vasya-zh/kampela-soldering-kit/kicad/base-board/images/base-board.png

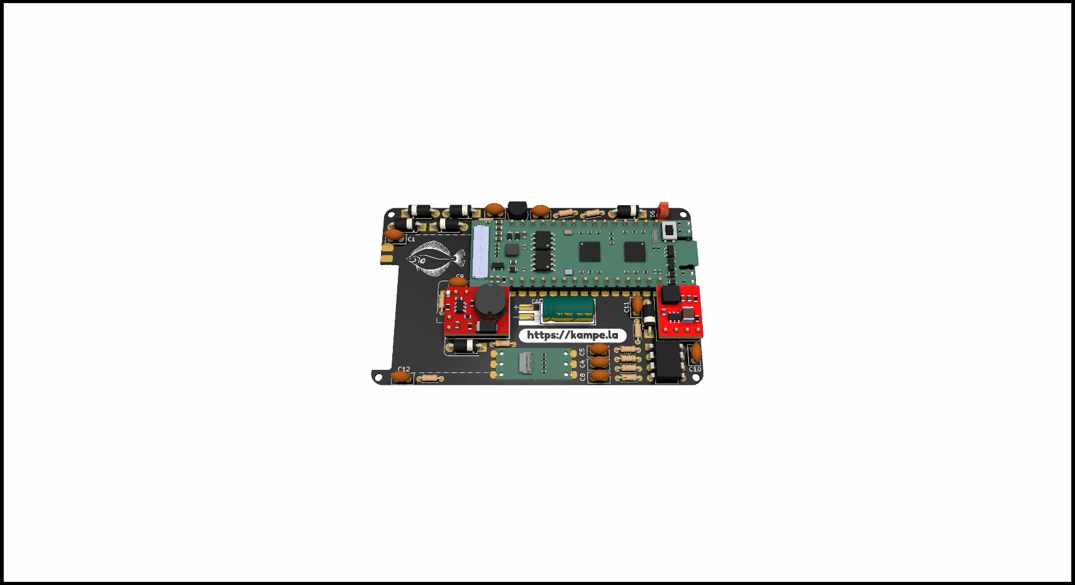
kicad/base-board/images/base-board.png
