vasya-zh/kampela-soldering-kit/kicad/base-board/images/bottom.png

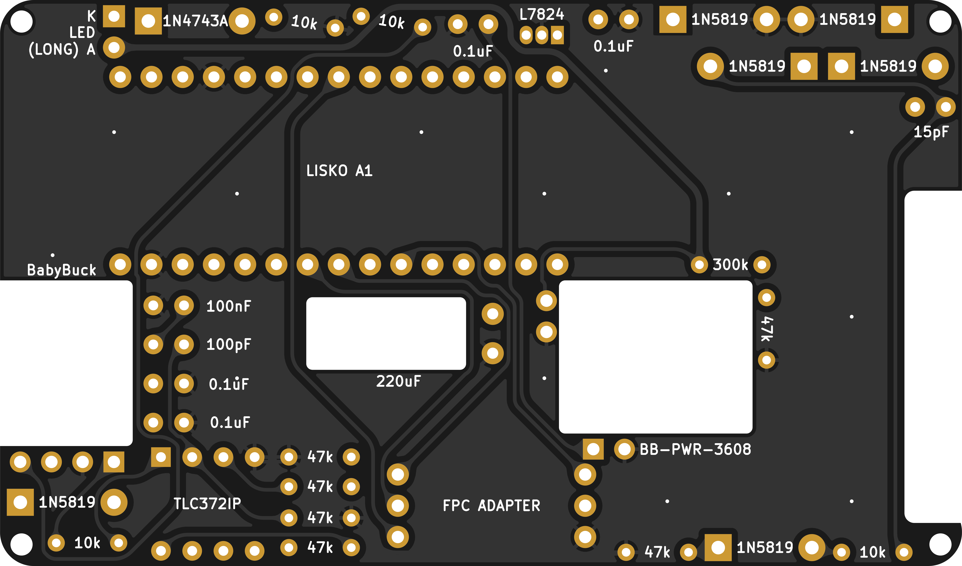
kicad/base-board/images/bottom.png
