vasya-zh/kampela-soldering-kit/kicad/base-board/images/top.png

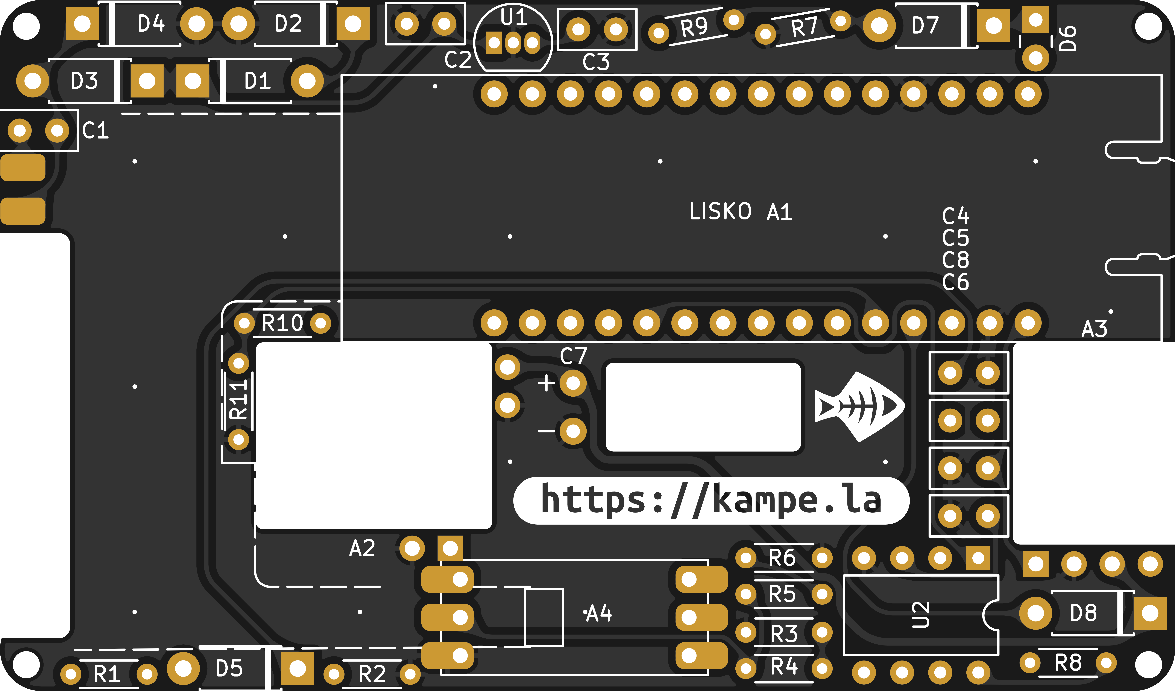
kicad/base-board/images/top.png
