vasya-zh/kampela-soldering-kit/kicad/flex-coil8/images/bottom.png

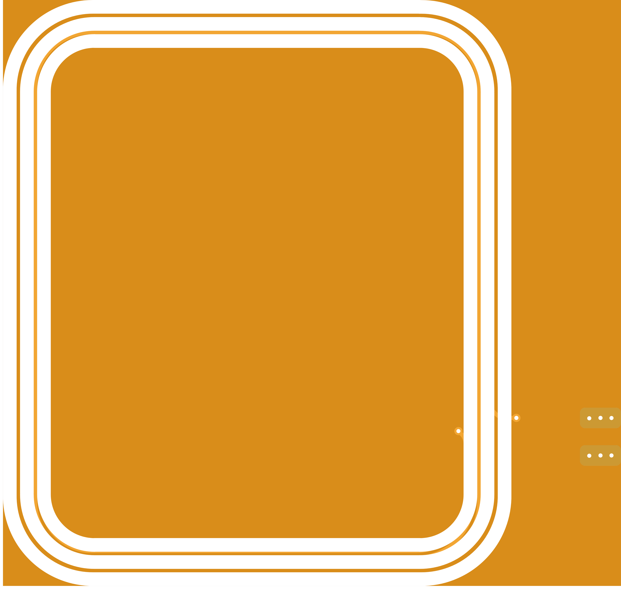
kicad/flex-coil8/images/bottom.png
