vasya-zh/kampela-soldering-kit/kicad/flex-coil8/images/flex-coil8.png

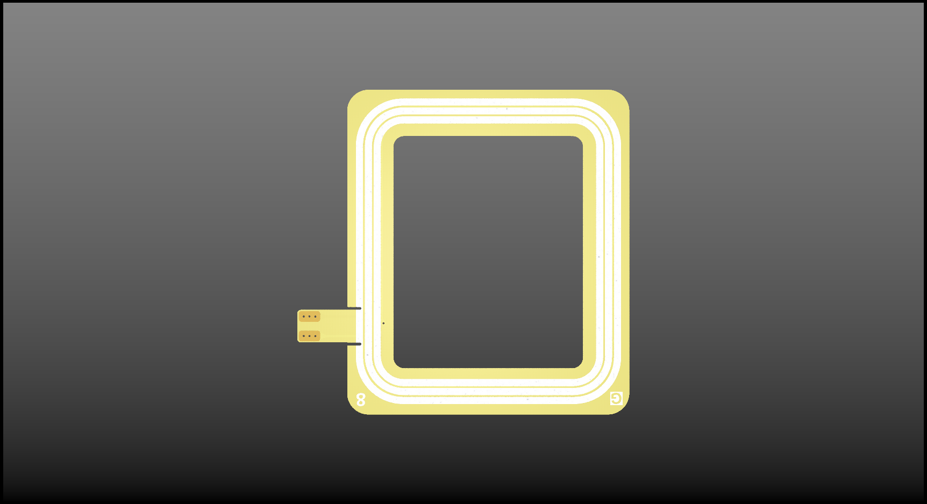
kicad/flex-coil8/images/flex-coil8.png
