vasya-zh/kampela-soldering-kit/kicad/flex-coil8/images/top.png

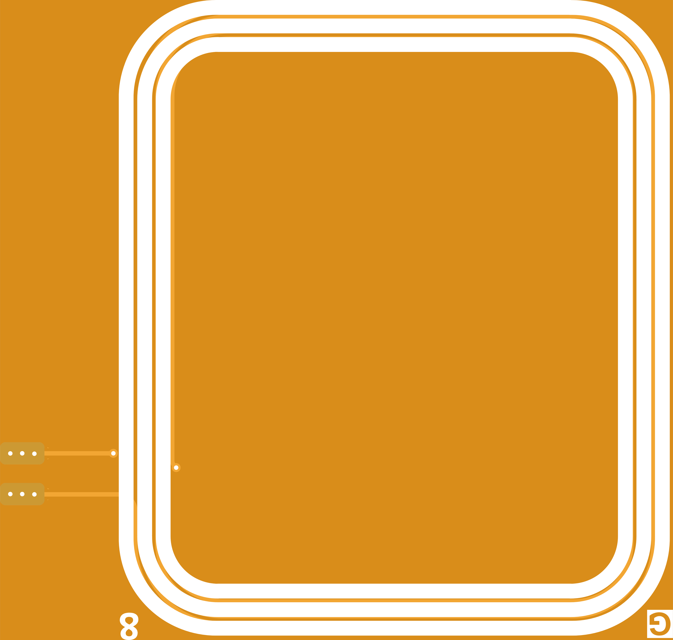
kicad/flex-coil8/images/top.png
