vasya-zh/kampela-soldering-kit/kicad/tag/images/bottom.png

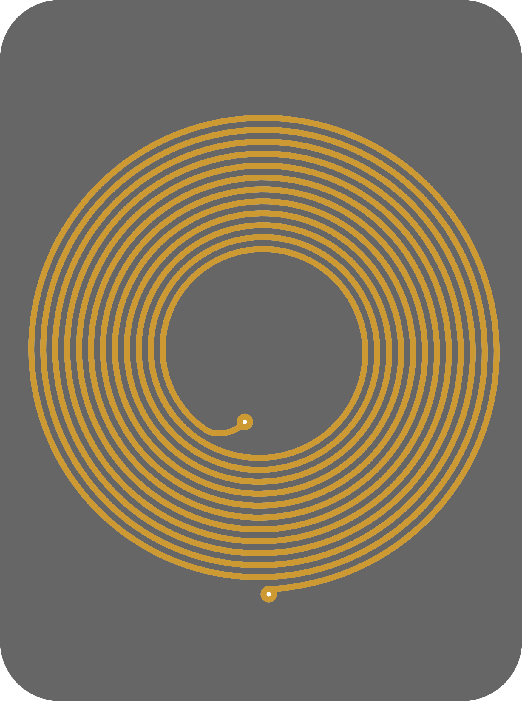
kicad/tag/images/bottom.png
