vasya-zh/kampela-soldering-kit/kicad/tag/images/top.png

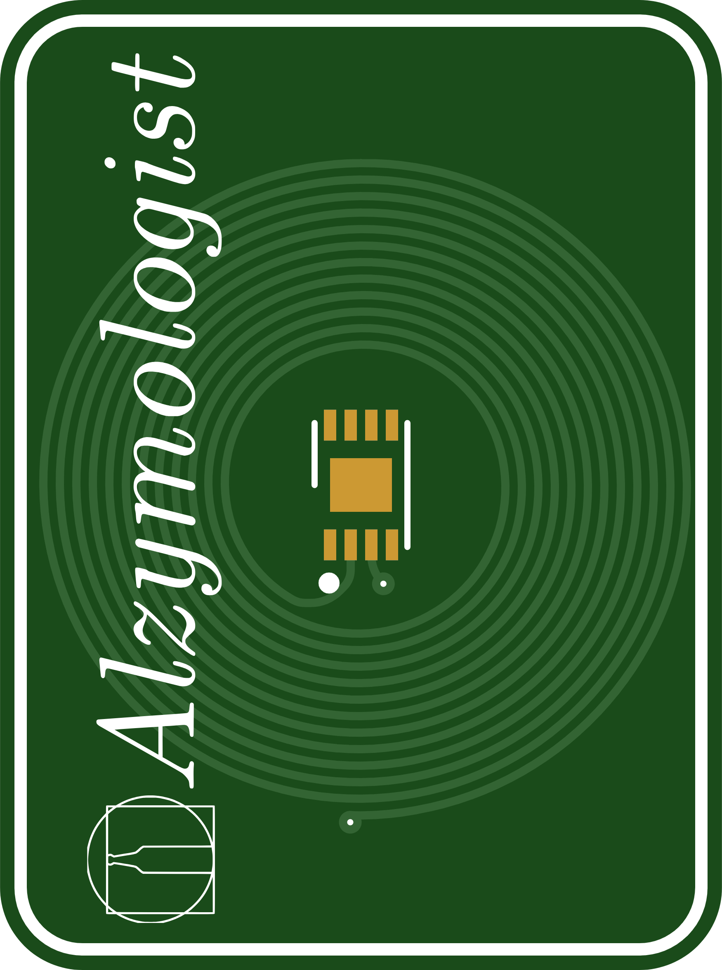
kicad/tag/images/top.png
