vasya-zh/kampela-soldering-kit/kicad/touch-6pin-adapter/images/bottom.png

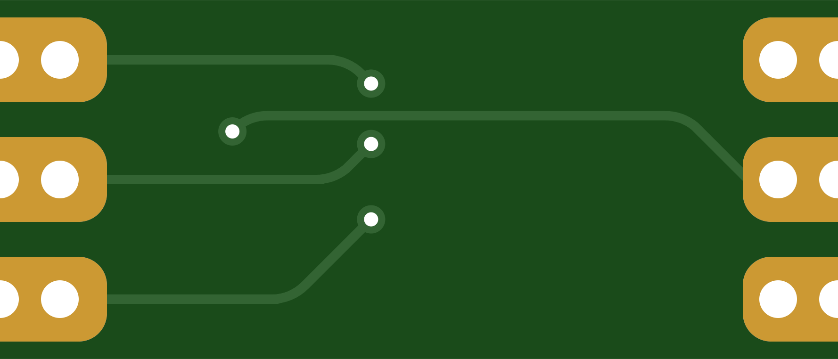
kicad/touch-6pin-adapter/images/bottom.png
