vasya-zh/kampela-soldering-kit/kicad/touch-6pin-adapter/images/top.png

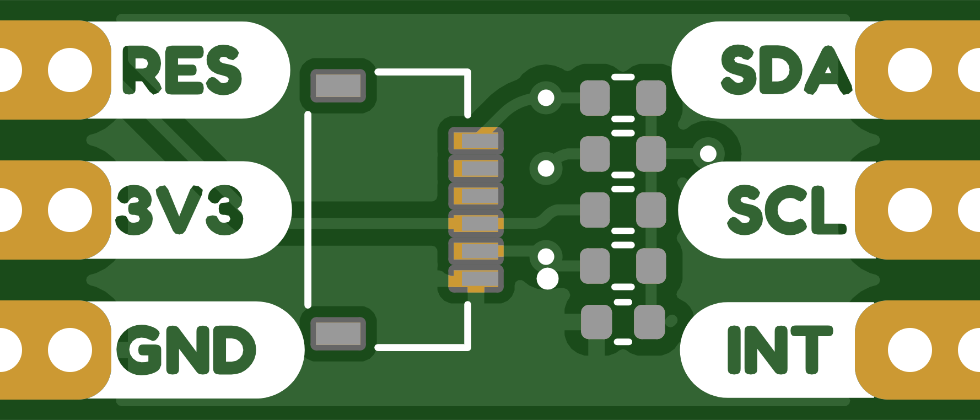
kicad/touch-6pin-adapter/images/top.png
