vasya-zh/kampela-soldering-kit/kicad/touch-6pin-adapter/images/touch-6pin-adapter.png

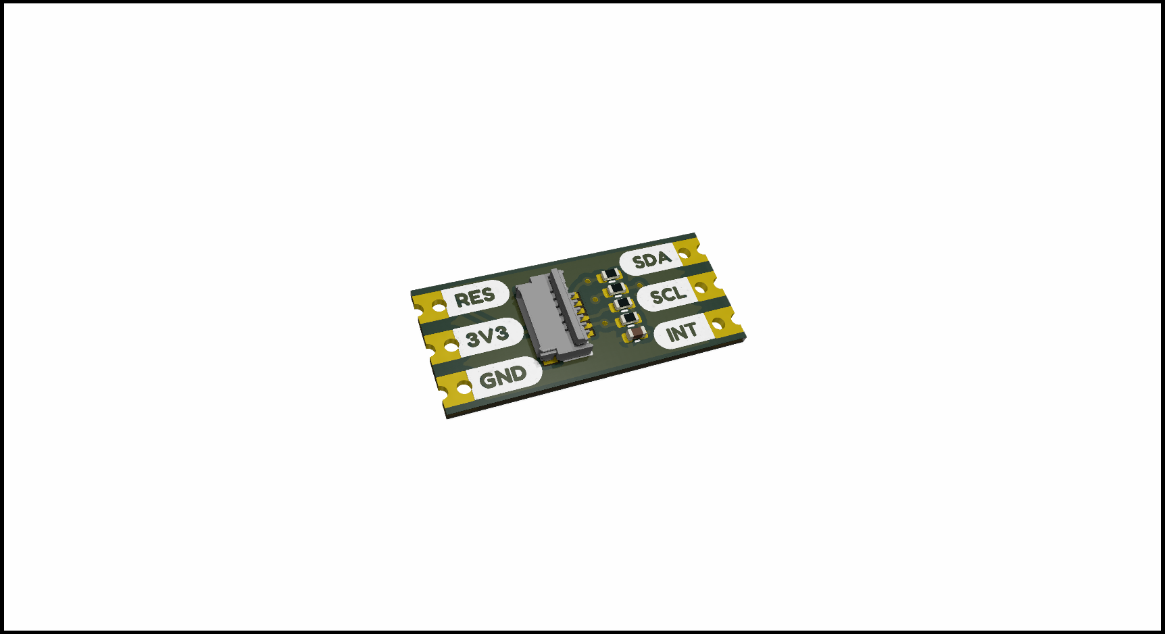
kicad/touch-6pin-adapter/images/touch-6pin-adapter.png
