vasya-zh/kampela-soldering-kit/kicad/base-board/images/02_base-board-power-modules-installed.png

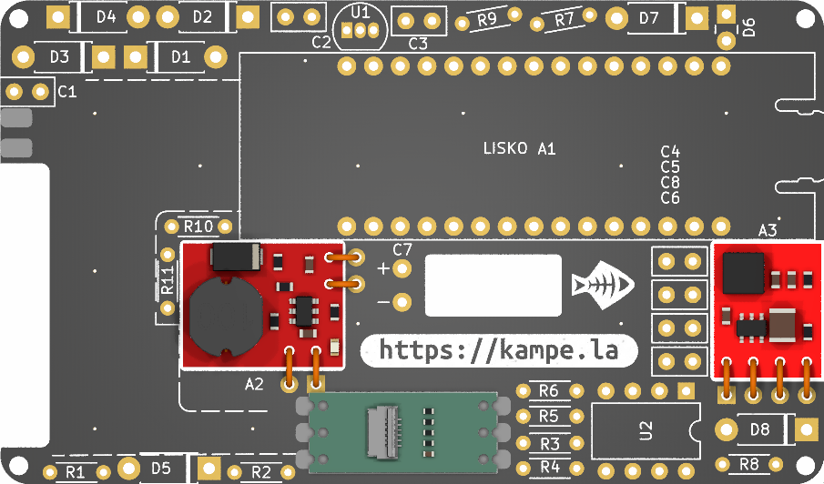
kicad/base-board/images/02_base-board-power-modules-installed.png
