vasya-zh/kampela-soldering-kit/kicad/base-board/images/06_base-board-IC-installed.png

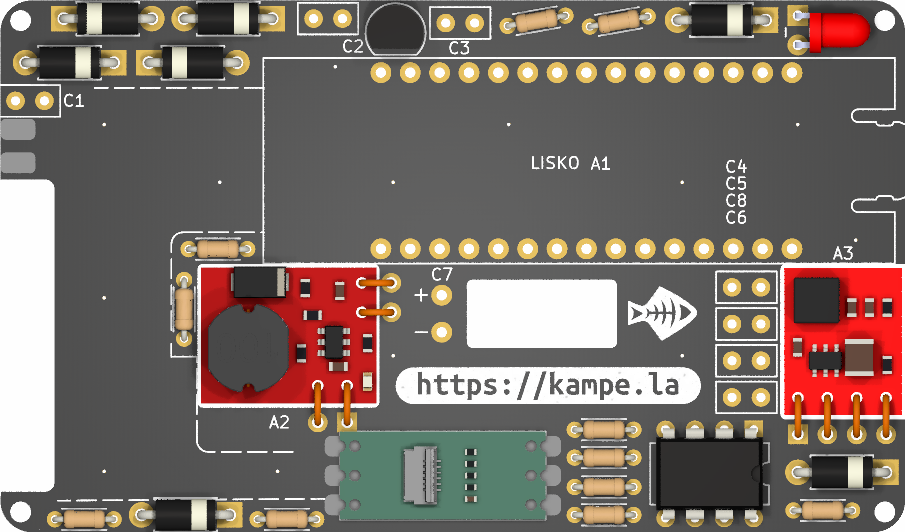
kicad/base-board/images/06_base-board-IC-installed.png
